mskk1122/OrcaRouter-ai-cube/artifacts/faces/expressions.gif

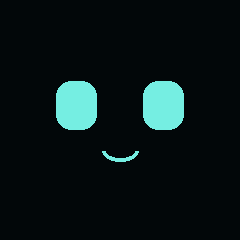
artifacts/faces/expressions.gif
